valfranciscangeli/proyecto-fd-mesa-de-extension-maquina-coser/img/aguja_con_mesa_base.jpg

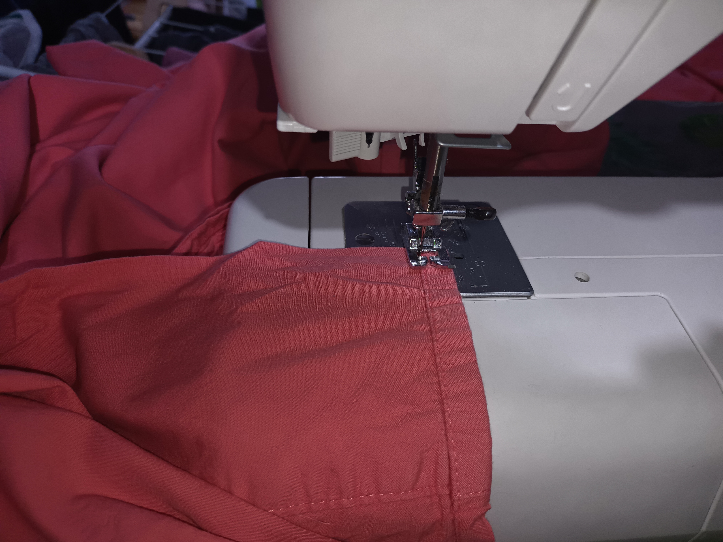
img/aguja_con_mesa_base.jpg
