valfranciscangeli/proyecto-fd-mesa-de-extension-maquina-coser/img/detalle_bottom.jpg

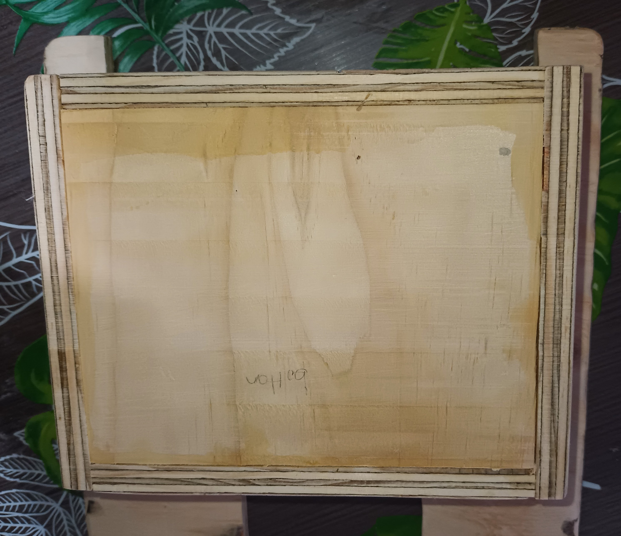
img/detalle_bottom.jpg
