valfranciscangeli/proyecto-fd-mesa-de-extension-maquina-coser/img/maquina.jpg

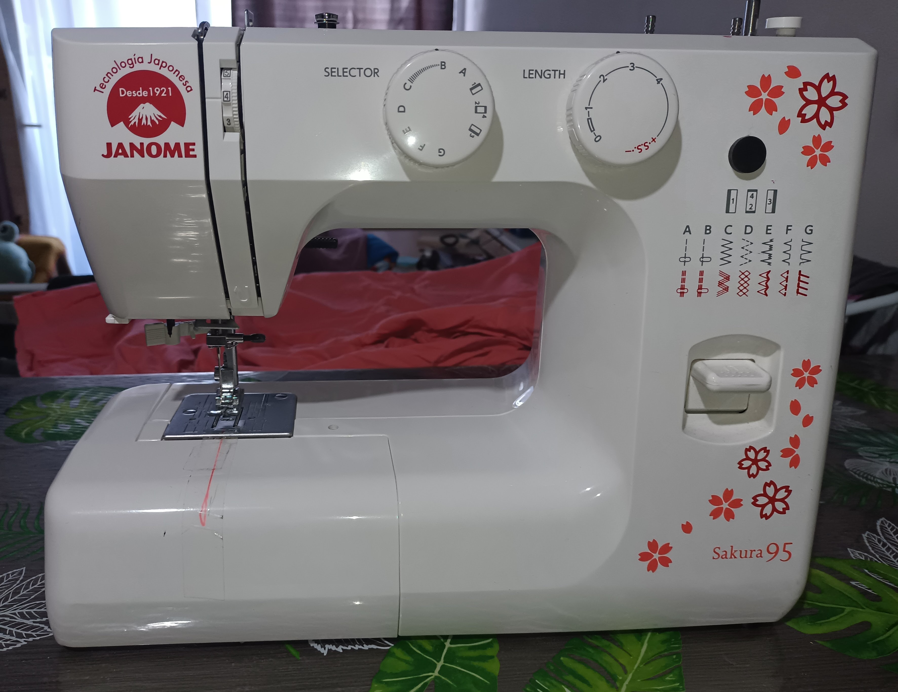
img/maquina.jpg
