valfranciscangeli/proyecto-fd-mesa-de-extension-maquina-coser/img/mesa_armada.jpg

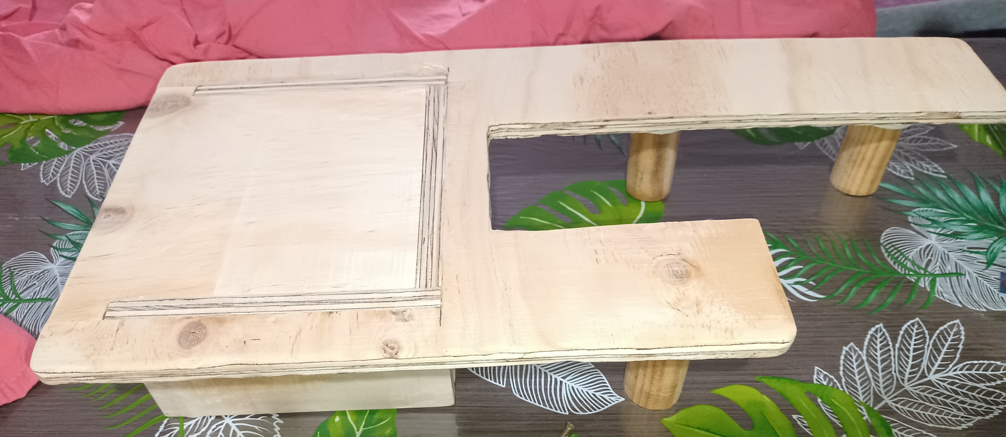
img/mesa_armada.jpg
