valfranciscangeli/proyecto-fd-mesa-de-extension-maquina-coser/img/problema_mesa_base.jpg

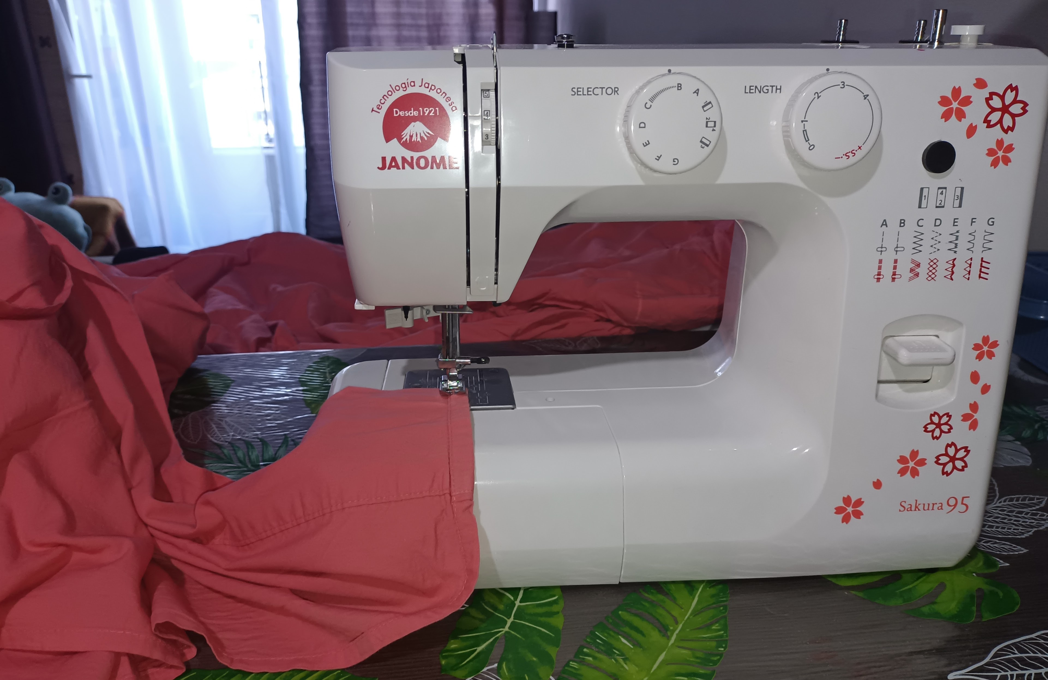
img/problema_mesa_base.jpg
