valfranciscangeli/proyecto-fd-mesa-de-extension-maquina-coser/img/tela_con_mesa_extension.jpg

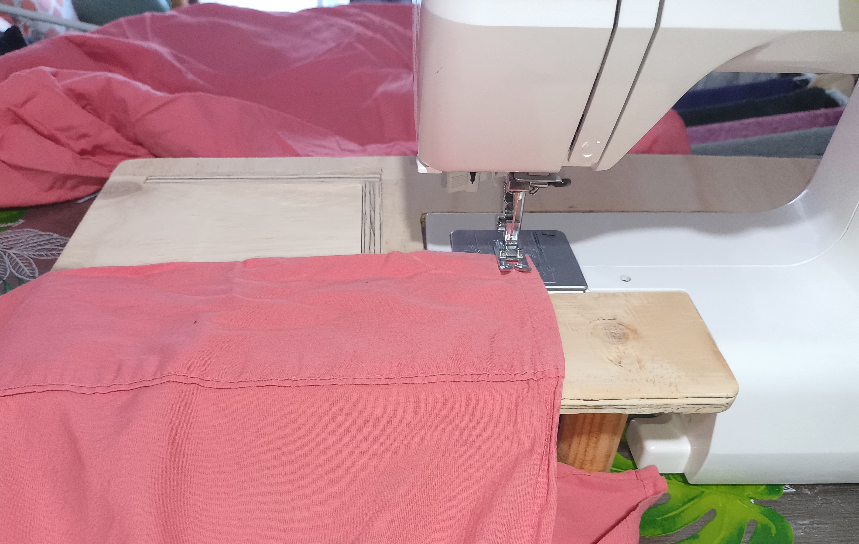
img/tela_con_mesa_extension.jpg
