valfranciscangeli/proyecto-fd-mesa-de-extension-maquina-coser/img/tela_sobre_extension.jpg

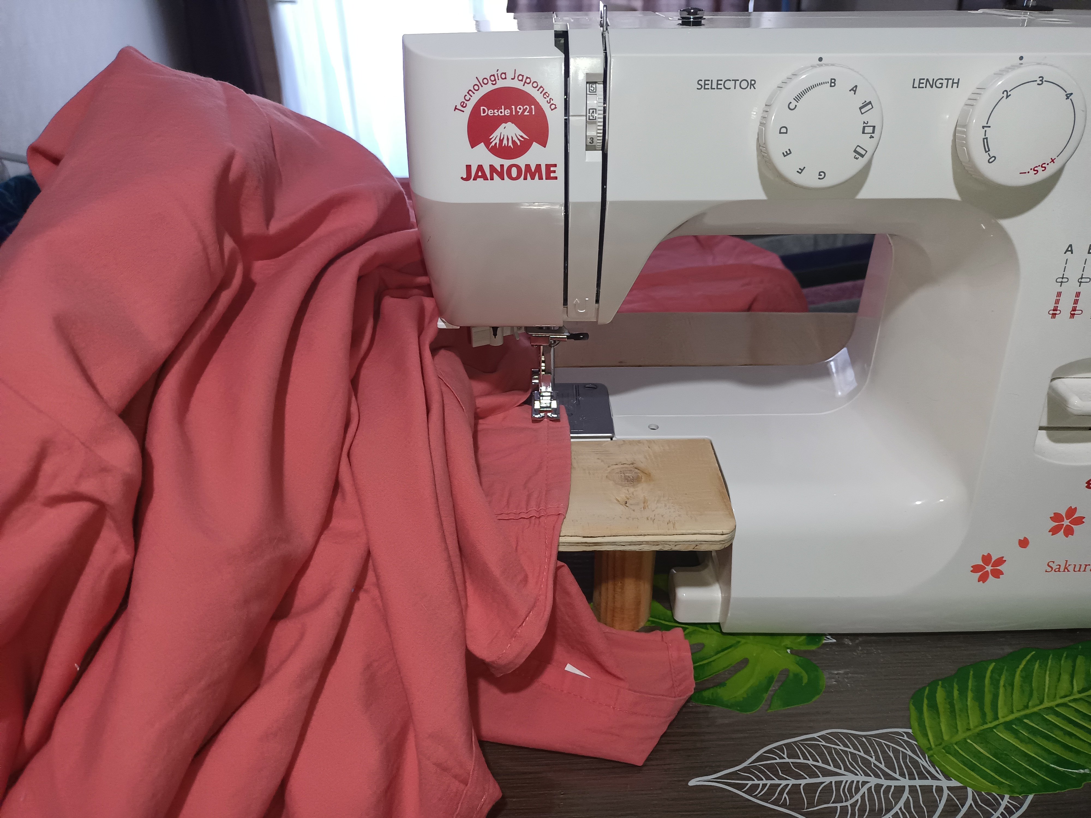
img/tela_sobre_extension.jpg
